firestaradmin/ShaoBing-No.1/Code/ShaoBing_No_1_F103C8T6/Drive/codetab.h

/************************************************************************************
*OLED SSD1306 字库

*Author : firestaradmin
* Copyright 2019 LXG
*
*PS:
*************************************************************************************/


#define GB16_CODE_NUM 35  //字库里的字个数
// ------------------  汉字字模的数据结构定义 ------------------------ //
struct  typFNT_GB16             // 汉字字模数据结构
{
       unsigned char Index[2];              // 汉字内码索引
       char Msk[32];                      // 点阵码数据
};

/////////////////////////////////////////////////////////////////////////
// 汉字字模表                                                          //
// Font:黑体16, 纵向取模上高位,数据排列:从上到下从左到右               //
/////////////////////////////////////////////////////////////////////////
const struct typFNT_GB16  GB_16[] =        // 数据表
{
"中", 0x00,0x00,0x00,0x00,0x0F,0xF0,0x08,0x20,
      0x08,0x20,0x08,0x20,0x08,0x20,0xFF,0xFF,
      0x08,0x20,0x08,0x20,0x08,0x20,0x08,0x20,
      0x0F,0xF0,0x00,0x00,0x00,0x00,0x00,0x00,

"国", 0x00,0x00,0x7F,0xFF,0x40,0x02,0x48,0x12,
      0x49,0x12,0x49,0x12,0x49,0x12,0x4F,0xF2,
      0x49,0x12,0x49,0x52,0x49,0x32,0x48,0x12,
      0x40,0x02,0x7F,0xFF,0x00,0x00,0x00,0x00,

"计", 0x02,0x00,0x02,0x00,0x42,0x00,0x33,0xFE,
      0x00,0x04,0x02,0x08,0x02,0x00,0x02,0x00,
      0x02,0x00,0xFF,0xFF,0x02,0x00,0x02,0x00,
      0x02,0x00,0x02,0x00,0x02,0x00,0x00,0x00,

"量", 0x04,0x00,0x04,0x01,0x04,0x01,0x7D,0xF5,
      0x55,0x55,0x55,0x55,0x55,0x55,0x55,0xFF,
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
	0xFC,0x00,0x3C,0x00,0x00,
	0x18,0x00,0x00,0x00,0x00,
	0x00,0x00,0x00,0x00,0x00,
	0x00,

	0x00,0x08,0x00,0x00,0x18,  // -~-
	0x00,0x00,0x30,0x00,0x00,
	0x20,0x00,0x00,0x30,0x00,
	0x00,0x10,0x00,0x00,0x08,
	0x00,0x00,0x0C,0x00,0x00,
	0x04,0x00,0x00,0x0C,0x00,
	0x00,0x18,0x00,0x00,0x10,
	0x00,

	0x00,0x03,0x00,0x00,0x0F,  // --
	0x00,0x00,0x39,0x00,0x00,
	0xE1,0x00,0x03,0x81,0x00,
	0x0E,0x01,0x00,0x03,0x81,
	0x00,0x00,0xE1,0x00,0x00,
	0x39,0x00,0x00,0x0F,0x00,
	0x00,0x03,0x00,0x00,0x00,
	0x00,
};
