firestaradmin/ShaoBing-No.1/Code/ShaoBing_No_1_F103C8T6/User/BMP_data.h

//纵向取模上高位,数据排列:从上到下 从左到右
//E:\MarsCloud\Doc\Beautiful\计量\课程了啦\大三上\数字温度计课设-哨兵1号\Code\STM32F103C8T6_OLED12864_DS18B20\Doc\主界面.bmp(0)
const unsigned char Interface_Main[] =
{
      0xFF,0xFF,0xFF,0xFF,0xFF,0xFF,0xFE,0x00,
      0x80,0x00,0x00,0x00,0x00,0x00,0x06,0x00,
      0x80,0x00,0x00,0x00,0x00,0x00,0x06,0xFF,
      0x80,0xE0,0x00,0x00,0x00,0x01,0xF6,0xFF,
      0x80,0x10,0x00,0x00,0x00,0x01,0x16,0x01,
      0x84,0xE0,0x00,0x00,0x00,0x01,0xF6,0x01,
      0x88,0x00,0x00,0x00,0x00,0x00,0x06,0x01,
      0x9F,0xFF,0xFF,0xFF,0xFF,0xFF,0x06,0x00,
      0x88,0x00,0x00,0x00,0x00,0x01,0x06,0xC1,
      0x84,0x00,0x00,0x00,0x00,0x01,0x06,0x63,
      0x80,0x00,0x00,0x00,0x00,0x01,0x06,0x36,
      0x80,0x00,0x00,0x00,0x00,0x01,0x06,0x1C,
      0x80,0x00,0x00,0x00,0x00,0x01,0x06,0x36,
      0x80,0x00,0x00,0x00,0x00,0x01,0x06,0x63,
      0x80,0x00,0x00,0x00,0x00,0x01,0x06,0xC1,
      0x80,0x00,0x00,0x00,0x00,0x01,0x06,0x00,
      0x80,0x00,0x00,0x00,0x00,0x01,0x06,0x7E,
      0x80,0x00,0x00,0x00,0x00,0x01,0x06,0xFF,
      0x80,0x00,0x00,0x00,0x00,0x01,0x06,0x81,
      0x80,0x00,0x00,0x00,0x00,0x01,0x06,0x89,
      0x80,0x00,0x00,0x00,0x00,0x01,0x06,0x89,
      0x80,0x00,0x00,0x00,0x00,0x01,0x06,0x4F,
      0x80,0x00,0x00,0x00,0x00,0x01,0x06,0x00,
      0x80,0x00,0x00,0x00,0x00,0x01,0x06,0x00,
      0x80,0x00,0x00,0x00,0x00,0x01,0x06,0x00,
      0x80,0x00,0x00,0x00,0x00,0x01,0x06,0x00,
      0x80,0x00,0x00,0x00,0x00,0x01,0x06,0x00,
      0x80,0x00,0x00,0x00,0x00,0x01,0x06,0x00,
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
      0x60,0x00,0x00,0x00,0x00,0x00,0x00,0x06,
      0x60,0x00,0x00,0x00,0x00,0x00,0x00,0x06,
      0x60,0x00,0x00,0x00,0x00,0x00,0x00,0x06,
      0x60,0x00,0x00,0x00,0x00,0x00,0x00,0x06,
      0x60,0x00,0x00,0x00,0x00,0x00,0x00,0x06,
      0x60,0x00,0x00,0x00,0x00,0x00,0x00,0x06,
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
};
